meepodeep/OrangePiDeck/Component Steps/XT60_Hembra.STEP

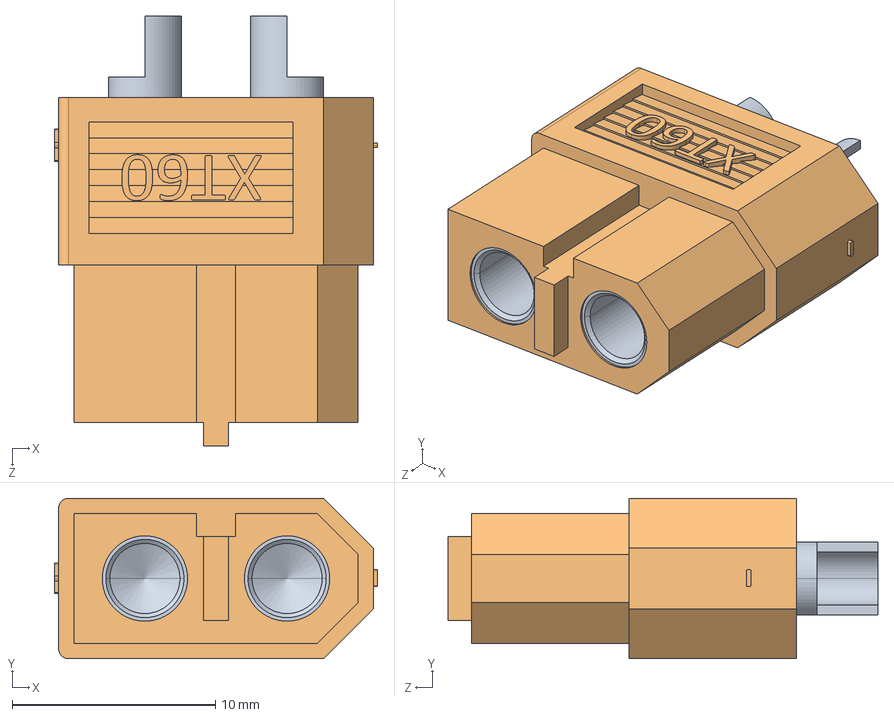
[picture p17: CAD file, 2025-06-03]
Component Steps/XT60_Hembra.STEP
15.9 x 7.90 x 21.1 mm
