meepodeep/OrangePiDeck/Final Print files/Exoskeleton/Screen Mount other half.stl

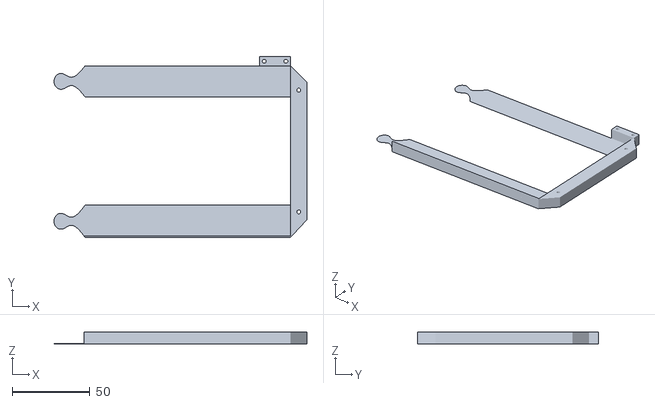
[picture p18: CAD file, 2025-06-03]
Final Print files/Exoskeleton/Screen Mount other half.stl
163.2 x 116.6 x 8.00
