meepodeep/OrangePiDeck/Component Steps/USB Type C Port (SMD Type).STEP

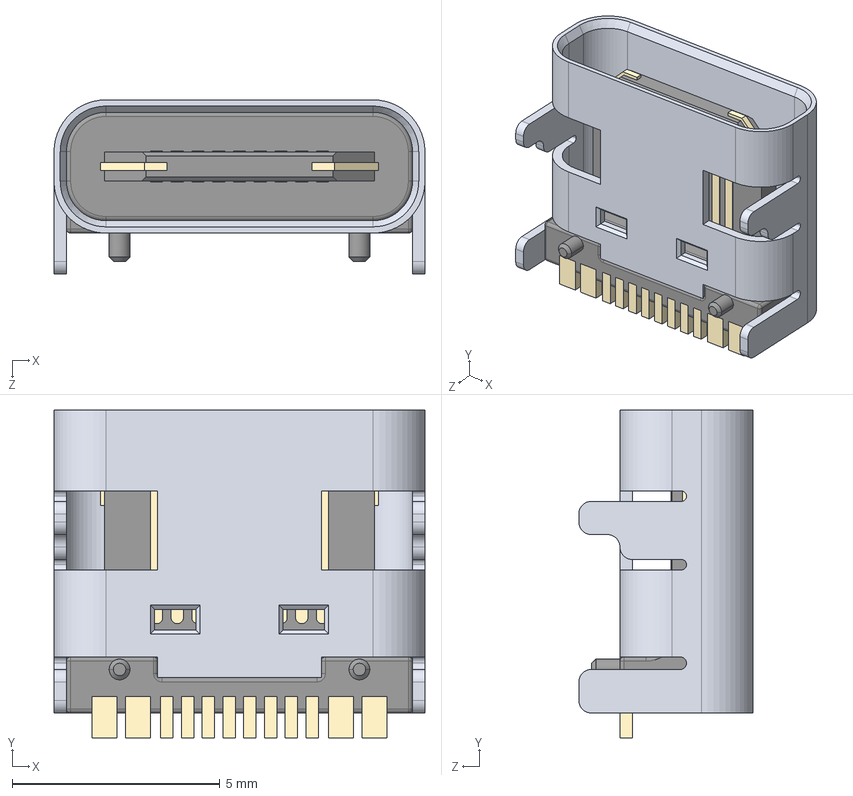
[picture p19: CAD file, 2025-06-03]
Component Steps/USB Type C Port (SMD Type).STEP
8.94 x 7.90 x 4.20 mm
