meepodeep/OrangePiDeck/Final Print files/Exoskeleton/Screen Mount.stl

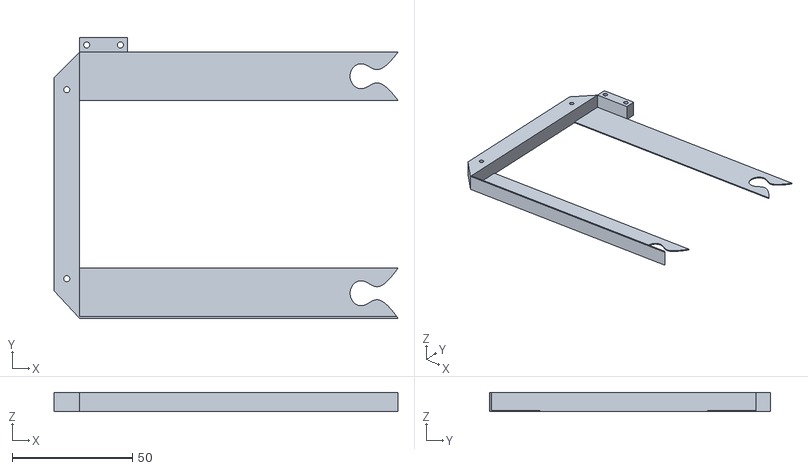
[picture p20: CAD file, 2025-06-03]
Final Print files/Exoskeleton/Screen Mount.stl
143.0 x 116.6 x 8.00
