meepodeep/OrangePiDeck/Component Steps/Case.3mf

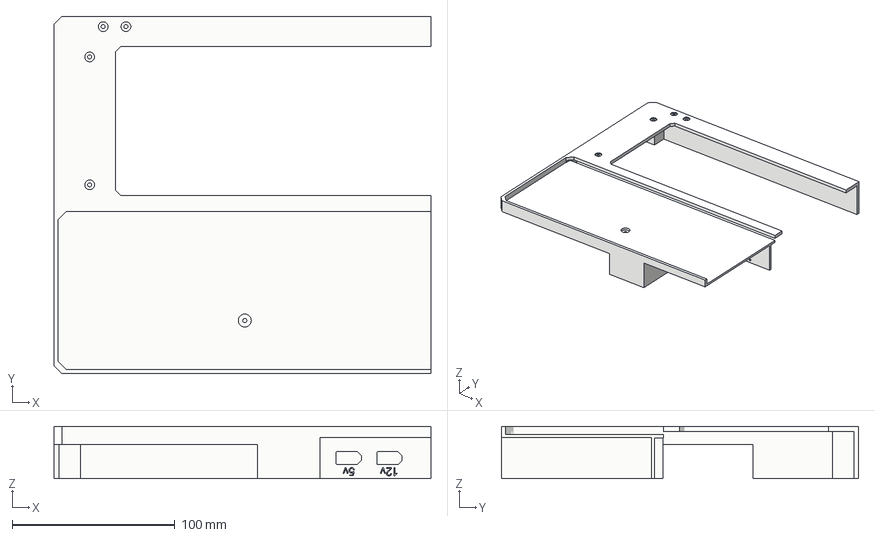
[picture p21: CAD file, 2025-06-03]
Component Steps/Case.3mf
231.6 x 219.6 x 32.0 mm
