meepodeep/OrangePiDeck/Final Print files/Exoskeleton/Back case.stl

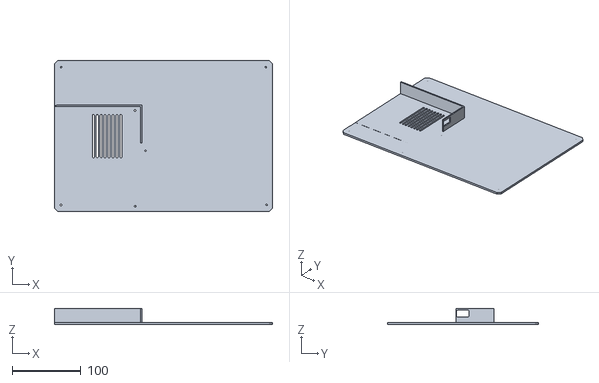
[picture p22: CAD file, 2025-06-03]
Final Print files/Exoskeleton/Back case.stl
317.1 x 219.6 x 23.8
