meepodeep/OrangePiDeck/Component Steps/Screen Mount.3mf

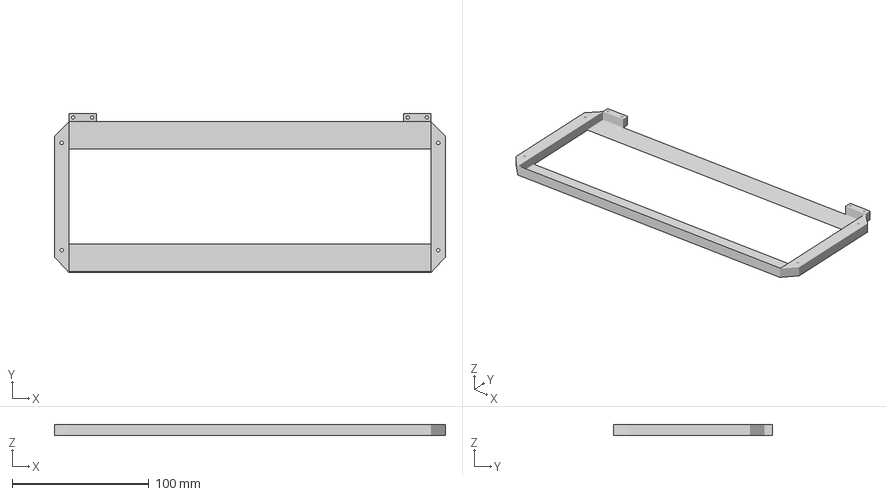
[picture p23: CAD file, 2025-06-03]
Component Steps/Screen Mount.3mf
286.4 x 116.6 x 8.00 mm
