meepodeep/OrangePiDeck/Final Print files/Exoskeleton/Case.stl

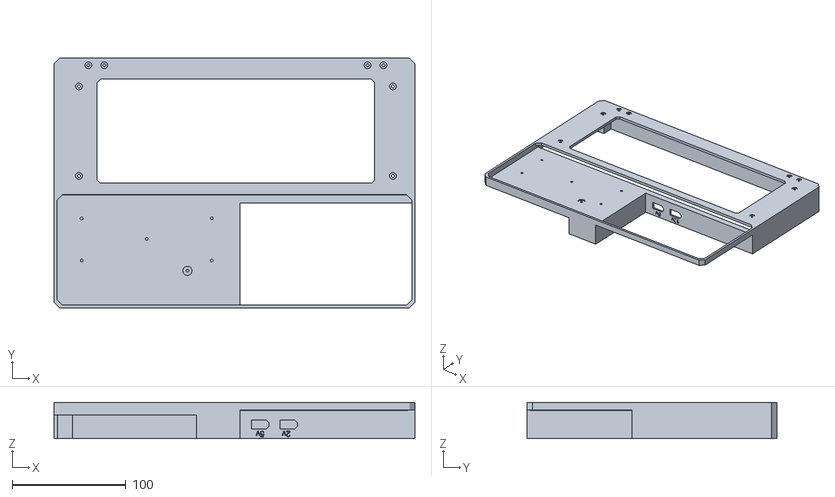
[picture p24: CAD file, 2025-06-03]
Final Print files/Exoskeleton/Case.stl
317.1 x 219.6 x 32.0
