meepodeep/OrangePiDeck/Component Steps/DC Power Jack 5.5mm x 2.1mm.STEP

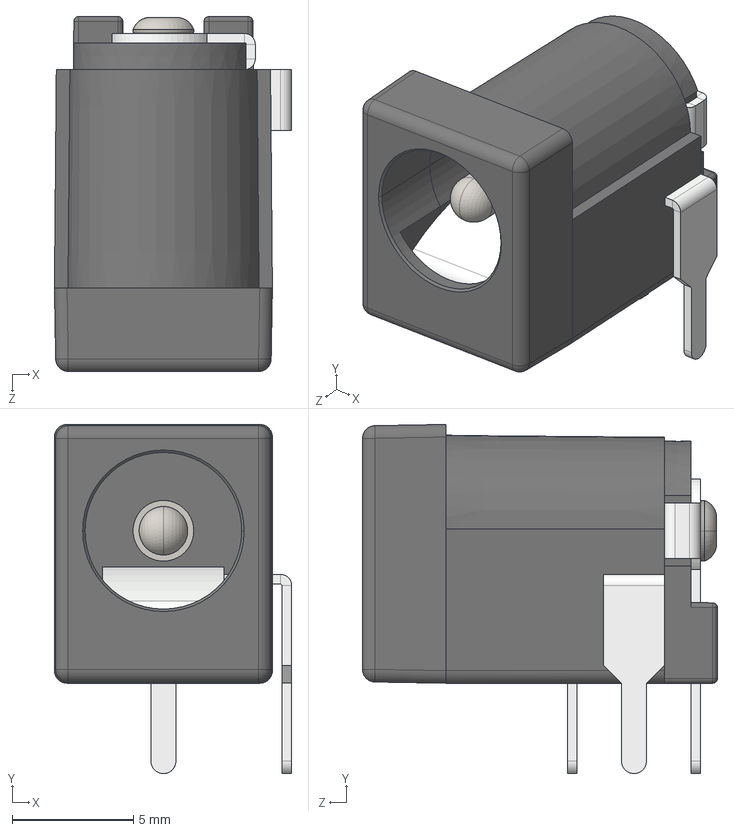
[picture p25: CAD file, 2025-06-03]
Component Steps/DC Power Jack 5.5mm x 2.1mm.STEP
9.77 x 14.4 x 14.6 mm
