meepodeep/OrangePiDeck/Component Steps/connecteurmagnetique.STEP

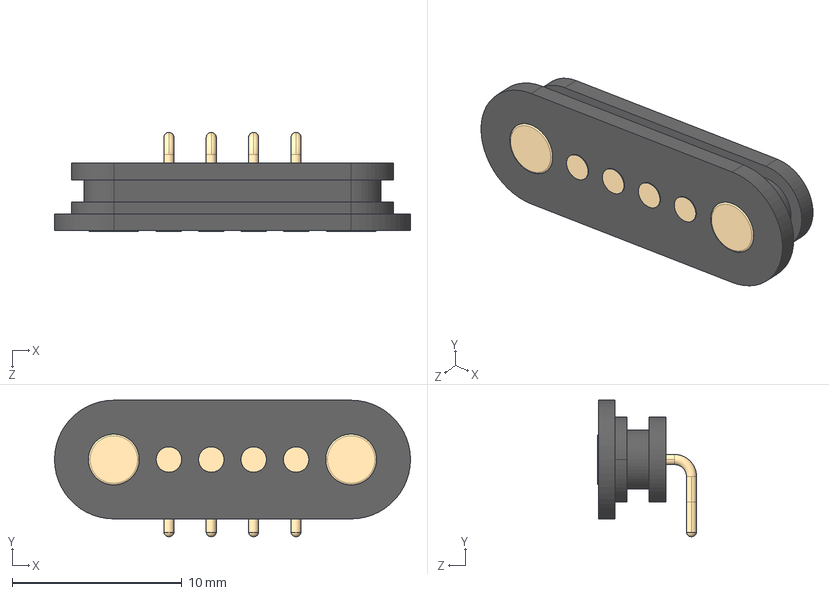
[picture p26: CAD file, 2025-06-03]
Component Steps/connecteurmagnetique.STEP
21.0 x 8.06 x 5.85 mm
plastique
contacts
pinout x 4
